josephyim224/elec3300/remote_sw/stm8s_conf.h

/**
  ******************************************************************************
  * @file    stm8s_conf.h
  * @author  MCD Application Team
  * @version V2.3.0
  * @date    16-June-2017
  * @brief   This file is used to configure the Library.
  ******************************************************************************
  * @attention
  *
  * <h2><center>&copy; COPYRIGHT 2014 STMicroelectronics</center></h2>
  *
  * Licensed under MCD-ST Liberty SW License Agreement V2, (the "License");
  * You may not use this file except in compliance with the License.
  * You may obtain a copy of the License at:
  *
  *        http://www.st.com/software_license_agreement_liberty_v2
  *
  * Unless required by applicable law or agreed to in writing, software 
  * distributed under the License is distributed on an "AS IS" BASIS, 
  * WITHOUT WARRANTIES OR CONDITIONS OF ANY KIND, either express or implied.
  * See the License for the specific language governing permissions and
  * limitations under the License.
  *
  ******************************************************************************
  */

/* Define to prevent recursive inclusion -------------------------------------*/
#ifndef __STM8S_CONF_H
#define __STM8S_CONF_H

/* Includes ------------------------------------------------------------------*/
#include "stm8s.h"

/* Uncomment the line below to enable peripheral header file inclusion */
#if defined(STM8S105) || defined(STM8S005) || defined(STM8S103) || defined(STM8S003) || \
    defined(STM8S001) || defined(STM8S903) || defined(STM8AF626x) || defined(STM8AF622x)
#include "stm8s_adc1.h"
#endif /* (STM8S105) || (STM8S005) || (STM8S103) || (STM8S003) || (STM8S001) || (STM8S903) || (STM8AF626x) || (STM8AF622x) */
#if defined(STM8S208) || defined(STM8S207) || defined(STM8S007) || defined(STM8AF52Ax) || \
    defined(STM8AF62Ax)
#include "stm8s_adc2.h"
#endif /* (STM8S208) || (STM8S207) || (STM8S007) || (STM8AF52Ax) || (STM8AF62Ax) */
#include "stm8s_awu.h"
#include "stm8s_beep.h"
#if defined(STM8S208) || defined(STM8AF52Ax)
#include "stm8s_can.h"
#endif /* (STM8S208) || (STM8AF52Ax) */
#include "stm8s_clk.h"
#include "stm8s_exti.h"
#include "stm8s_flash.h"
#include "stm8s_gpio.h"
#include "stm8s_i2c.h"
#include "stm8s_itc.h"
#include "stm8s_iwdg.h"
#include "stm8s_rst.h"
#include "stm8s_spi.h"
#include "stm8s_tim1.h"
#if defined(STM8S208) || defined(STM8S207) || defined(STM8S007) || defined(STM8S103) ||                        \
    defined(STM8S003) || defined(STM8S001) || defined(STM8S105) || defined(STM8S005) || defined(STM8AF52Ax) || \
    defined(STM8AF62Ax) || defined(STM8AF626x)
#include "stm8s_tim2.h"
#endif /* (STM8S208) || (STM8S207) || (STM8S007) || (STM8S103) || (STM8S003) || (STM8S001) || (STM8S105) || (STM8S005) || (STM8AF52Ax) || (STM8AF62Ax) || (STM8AF626x) */
#if defined(STM8S208) || defined(STM8S207) || defined(STM8S007) || defined(STM8S105) || \
    defined(STM8S005) || defined(STM8AF52Ax) || defined(STM8AF62Ax) || defined(STM8AF626x)
#include "stm8s_tim3.h"
#endif /* (STM8S208) || (STM8S207) || (STM8S007) || (STM8S105) || (STM8S005) || (STM8AF52Ax) || (STM8AF62Ax) || (STM8AF626x) */
#if defined(STM8S208) || defined(STM8S207) || defined(STM8S007) || defined(STM8S103) ||                        \
    defined(STM8S003) || defined(STM8S001) || defined(STM8S105) || defined(STM8S005) || defined(STM8AF52Ax) || \
    defined(STM8AF62Ax) || defined(STM8AF626x)
#include "stm8s_tim4.h"
#endif                                       /* (STM8S208) || (STM8S207) || (STM8S007) || (STM8S103) || (STM8S003) || (STM8S001) || (STM8S105) || (STM8S005) || (STM8AF52Ax) || (STM8AF62Ax) || (STM8AF626x) */
#if defined(STM8S903) || defined(STM8AF622x) /* SDCC patch: see https://github.com/tenbaht/sduino/tree/master/STM8S_StdPeriph_Driver */
#include "stm8s_tim5.h"
#include "stm8s_tim6.h"
#endif /* (STM8S903) || (STM8AF622x) */
#if defined(STM8S208) || defined(STM8S207) || defined(STM8S007) || defined(STM8S103) || \
    defined(STM8S003) || defined(STM8S001) || defined(STM8S903) || defined(STM8AF52Ax) || defined(STM8AF62Ax)
#include "stm8s_uart1.h"
#endif /* (STM8S208) || (STM8S207) || (STM8S007) || (STM8S103) || (STM8S003) || (STM8S001) || (STM8S903) || (STM8AF52Ax) || (STM8AF62Ax) */
#if defined(STM8S105) || defined(STM8S005) || defined(STM8AF626x)
#include "stm8s_uart2.h"
#endif /* (STM8S105) || (STM8S005) || (STM8AF626x) */
#if defined(STM8S208) || defined(STM8S207) || defined(STM8S007) || defined(STM8AF52Ax) || \
    defined(STM8AF62Ax)
#include "stm8s_uart3.h"
#endif                  /* (STM8S208) || (STM8S207) || (STM8S007) || (STM8AF52Ax) || (STM8AF62Ax) */
#if defined(STM8AF622x) /* SDCC patch: see https://github.com/tenbaht/sduino/tree/master/STM8S_StdPeriph_Driver */
#include "stm8s_uart4.h"
#endif /* (STM8AF622x) */
#include "stm8s_wwdg.h"

/* Exported types ------------------------------------------------------------*/
/* Exported constants --------------------------------------------------------*/
/* Uncomment the line below to expanse the "assert_param" macro in the
   Standard Peripheral Library drivers code */
#define USE_FULL_ASSERT (1)

/* Exported macro ------------------------------------------------------------*/
#ifdef USE_FULL_ASSERT

/**
  * @brief  The assert_param macro is used for function's parameters check.
  * @param expr: If expr is false, it calls assert_failed function
  *   which reports the name of the source file and the source
  *   line number of the call that failed.
  *   If expr is true, it returns no value.
  * @retval : None
  */
#define assert_param(expr) ((expr) ? (void)0 : assert_failed((uint8_t *)__FILE__, __LINE__))
/* Exported functions ------------------------------------------------------- */
void assert_failed(uint8_t *file, uint32_t line);
#else
#define assert_param(expr) ((void)0)
#endif /* USE_FULL_ASSERT */

#endif /* __STM8S_CONF_H */

/************************ (C) COPYRIGHT STMicroelectronics *****END OF FILE****/
